mariusenglund/three-phase-inverter/pcb-design-files/LIB-3D/74LV1T34GV-Q100H.stp

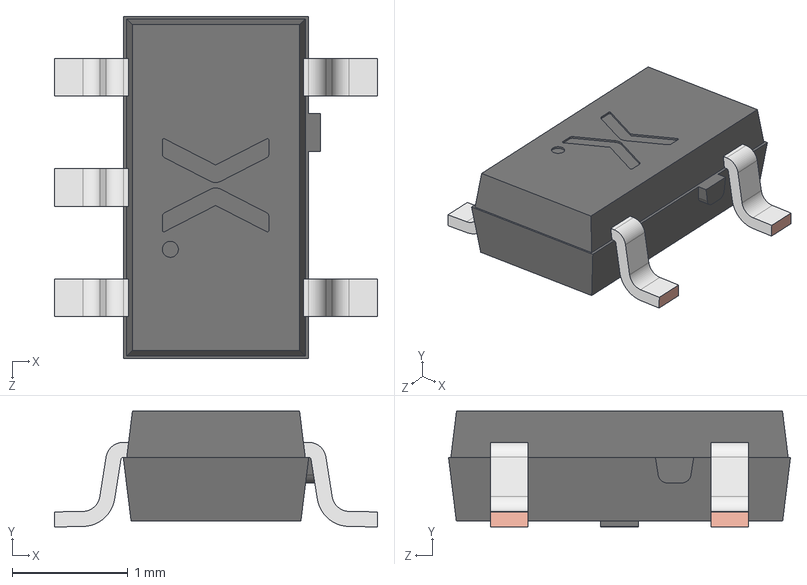
[picture p32: CAD file, 2023-10-15]
pcb-design-files/LIB-3D/74LV1T34GV-Q100H.stp
2.79 x 1.00 x 2.95 mm
SOT753 Lower mold body
SOT753 Lead x 5
SOT753 Upper mold body
