mariusenglund/three-phase-inverter/pcb-design-files/LIB-3D/DC-link-capacitor-B32776G0146K000.stp

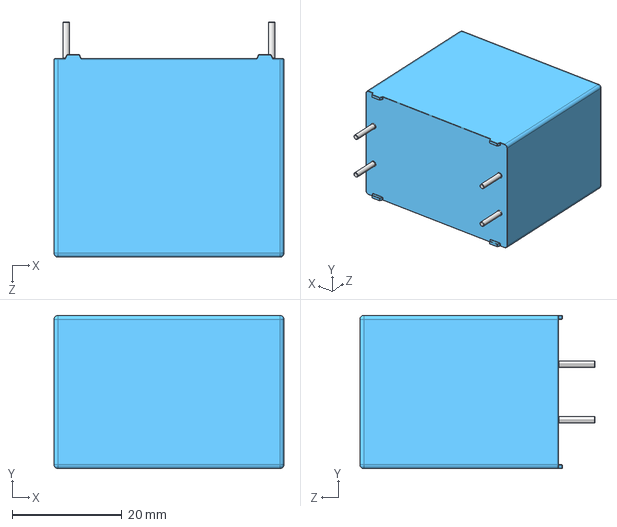
[picture p33: CAD file, 2023-10-15]
pcb-design-files/LIB-3D/DC-link-capacitor-B32776G0146K000.stp
42.0 x 28.0 x 43.0 mm
