mariusenglund/three-phase-inverter/pcb-design-files/LIB-3D/Keystone - 5019 - PCB Test Point v1.step

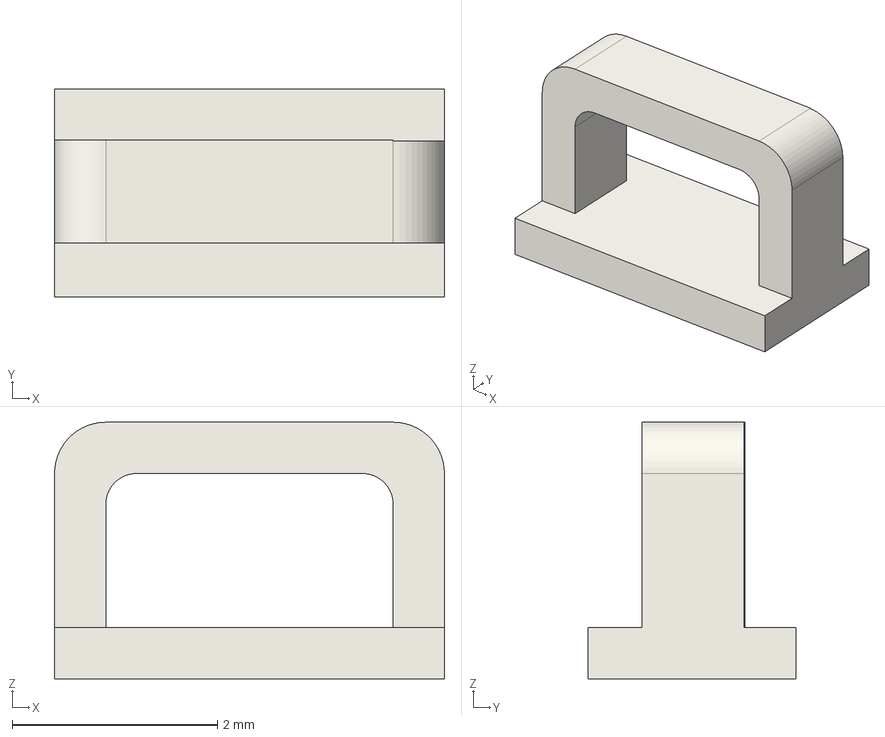
[picture p34: CAD file, 2023-10-15]
pcb-design-files/LIB-3D/Keystone - 5019 - PCB Test Point v1.step
3.80 x 2.03 x 2.50 mm
