mariusenglund/three-phase-inverter/pcb-design-files/LIB-3D/IR2118SPBF.stp

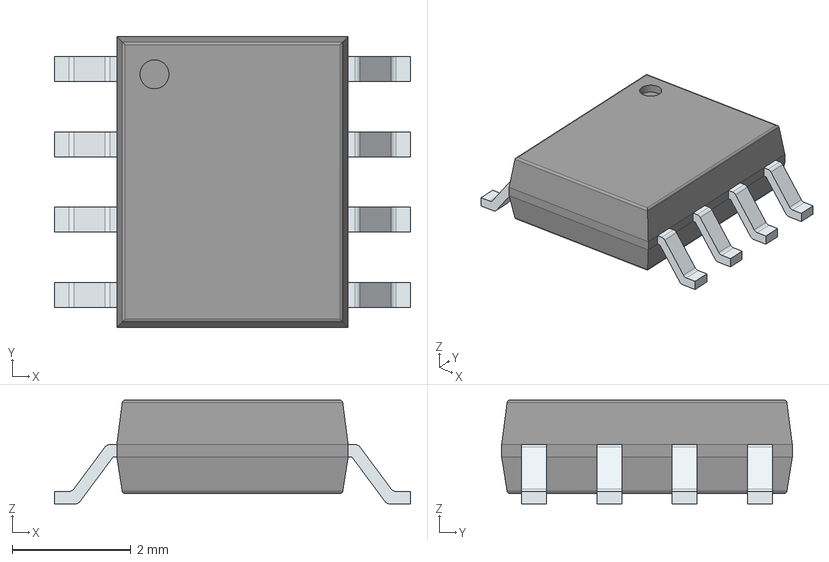
[picture p35: CAD file, 2023-10-15]
pcb-design-files/LIB-3D/IR2118SPBF.stp
6.00 x 4.90 x 1.75 mm
PinsArrayLR
