mariusenglund/three-phase-inverter/pcb-design-files/LIB-3D/C247-025-1VE.stp

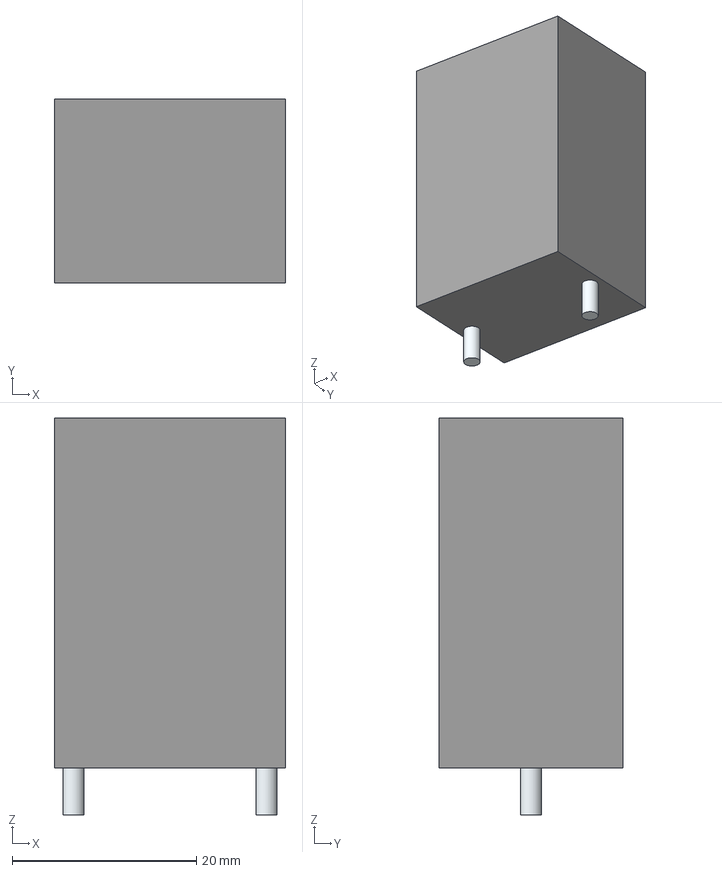
[picture p36: CAD file, 2023-10-15]
pcb-design-files/LIB-3D/C247-025-1VE.stp
25.1 x 19.9 x 43.1 mm
Leads x 2
