mariusenglund/three-phase-inverter/pcb-design-files/LIB-3D/Display_MC21605C6W-SPTLYI-V2.stp

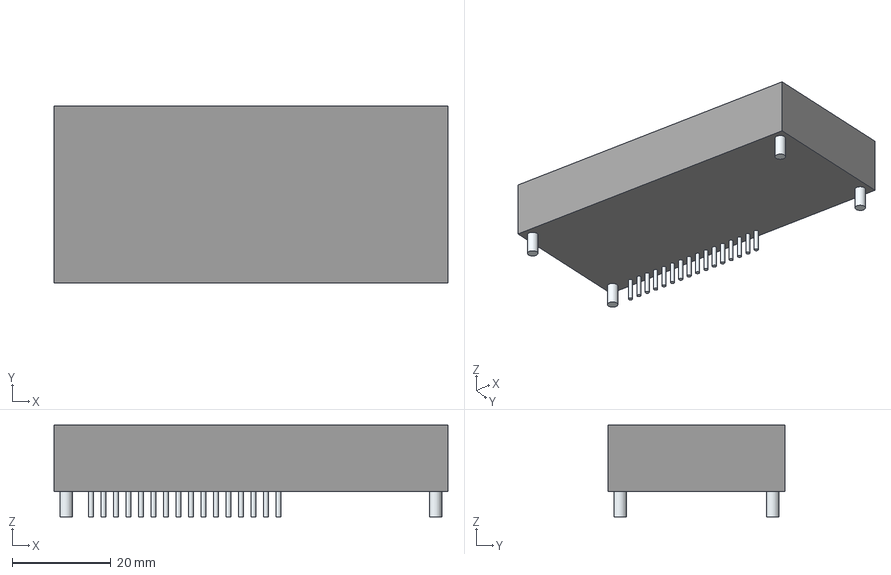
[picture p37: CAD file, 2023-10-15]
pcb-design-files/LIB-3D/Display_MC21605C6W-SPTLYI-V2.stp
80.0 x 36.0 x 18.6 mm
Leads
