mariusenglund/three-phase-inverter/pcb-design-files/LIB-3D/NTE0505MC.stp

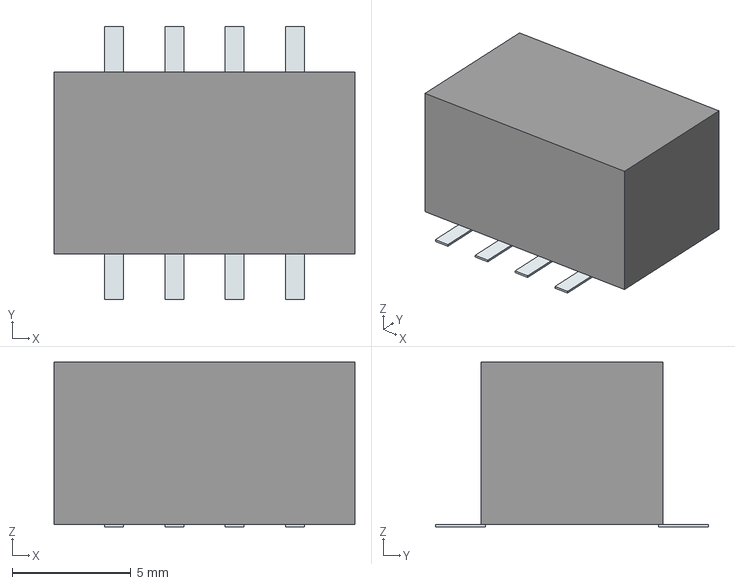
[picture p38: CAD file, 2023-10-15]
pcb-design-files/LIB-3D/NTE0505MC.stp
12.7 x 11.5 x 6.95 mm
Pins
