mariusenglund/three-phase-inverter/pcb-design-files/LIB-3D/B3F-5050.stp

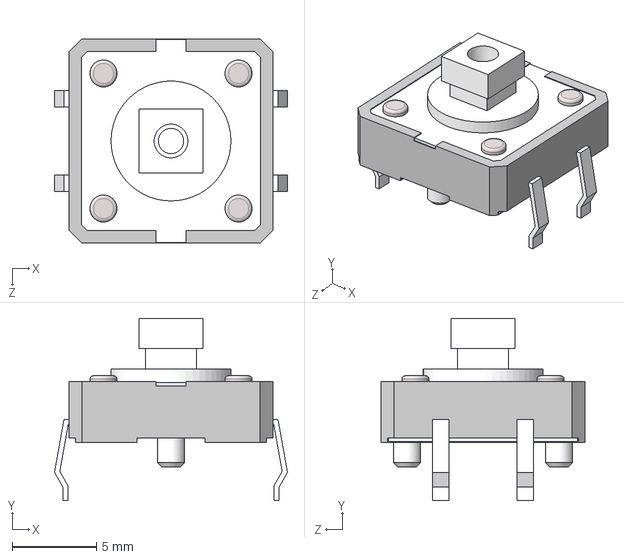
[picture p39: CAD file, 2023-10-15]
pcb-design-files/LIB-3D/B3F-5050.stp
13.8 x 10.8 x 12.1 mm
