mariusenglund/three-phase-inverter/pcb-design-files/LIB-3D/LED_red_SML-LX0805SIC-TR.stp

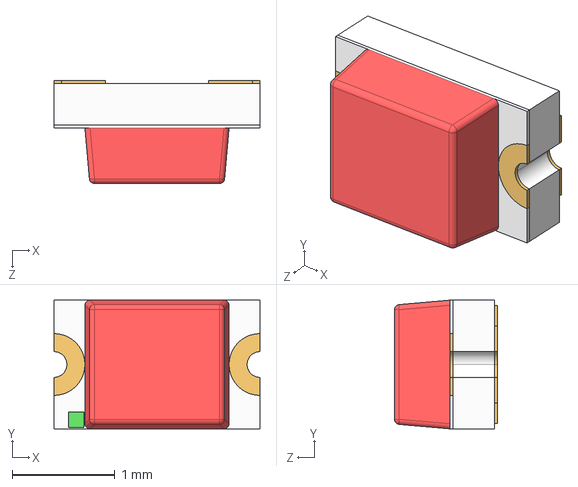
[picture p40: CAD file, 2023-10-15]
pcb-design-files/LIB-3D/LED_red_SML-LX0805SIC-TR.stp
2.00 x 1.25 x 1.00 mm
