mariusenglund/three-phase-inverter/simulation-files/gate-resistance-simulation/gate-resistance-simulation.asc

A1: diffschmitt; vt=0 vh=0.01 Vhigh=5 Vlow=0
A2: schmtinv
A3: schmtinv
A4: and
A5: and
B1: bv; V=V(ctrl_top_dt)*19 - 4
B2: bv; V=V(ctrl_bot_dt)*19-4
C1: cap; 1.3n
C2: cap; 1.3n
C3: cap; {C}
C4: cap; {C}
D3: diode
D4: diode
IGBT: IKW40N120H3_L1
L1: ind; 2.6m
R1: res; 60
R2: res; {Rgate}
R3: res; {Rgate}
R4: res; {R}
R5: res; 4.7k
R6: res; 4.7k
R7: res; {R}
U2: IKW40N120H3_L1
V1: voltage; {Ud2}
V2: voltage; PULSE(0 1 0 {Ts2} {Ts2} 0 {Ts})
V3: voltage; SINE(0.5 0.25 {fmod})
V4: voltage; {Ud2}
Named nets: 0, ctrl_top, ctrl_bot, ctrl_top_dt, ctrl_bot_dt, gate, C, E
.param Ts=1/fs
.param Ts2 = Ts/2
.param fmod=50
.param ma = 0.5
.param Ud2 = Ud/2
.param fs = 5000
.param Ud = 565
.param C = 14e-6
.param R=860k
Motor equivalent
DC-Link
.tran 0 0.4m 0.2m uic
.param Rgate = 75
