mariusenglund/three-phase-inverter/simulation-files/power-dissipation-simulation/power-dissipation-simulation.asc

D1: diode; VS-E5PH7506
I1: current; 5
R1: res; {Rgate}
U1: IKW40N120H3_L1
V1: voltage; PULSE(-8 15 0 1n 1n {ton} {ts})
Named nets: 0
.param D=0.5
.tran 1m
.param fs = 5k
.param ts = 1/fs
.param ton = ts*D
.param Rgate = 75
