mariusenglund/three-phase-inverter/source-code/include/bsp_timer.h

/* TIM1 */
void bsp_set_TIM1_frequency(uint32_t freq_clock, uint32_t freq_tick);
void bsp_set_TIM1_compare(uint16_t comp_CH1, uint16_t comp_CH2, uint16_t comp_CH3);

/* TIM2 */
void bsp_set_TIM2_frequency(uint32_t freq_clock, uint32_t freq_tick);
